ddugas5/hexapod/src/robot_description/meshes/rear_right_femur_link.STL

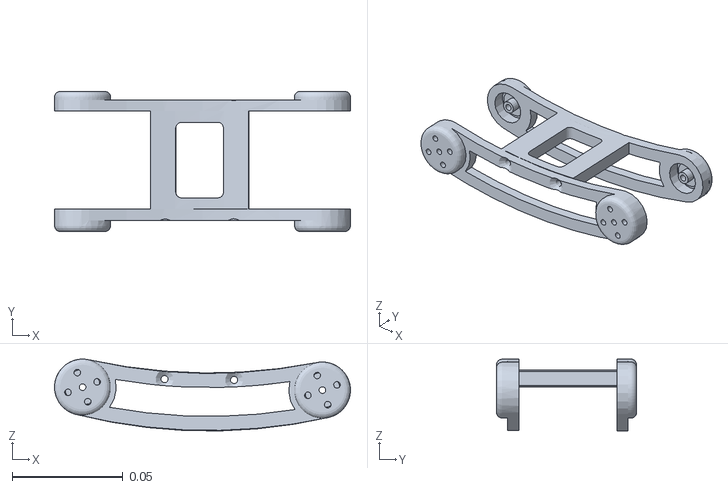
[picture p10: CAD file, 2026-01-09]
src/robot_description/meshes/rear_right_femur_link.STL
0.134 x 0.0634 x 0.0325
